arorasoham9/Embedded-C--ARM-M0-Cortex-Maze-game/src/wavetable.c

#include <math.h>

#include "midiplay.h"

short int wavetable[N];

// sine wave
void init_wavetable_sine(void) {
    int x;
    for(x=0; x<N; x++) {
        wavetable[x] = 32767 * sin(2 * M_PI * x / N);
    }
}

// sawtooth wave
void init_wavetable_sawtooth(void) {
    int x;
    for(x=0; x<N; x++)
        wavetable[x] = 32767.0 * (x - N/2) / (1.0*N);
}

// square wave
void init_wavetable_square(void) {
    int x;
    for(x=0; x<N; x++)
        if (x < N/2)
            wavetable[x] = -32767;
        else
            wavetable[x] = 32767;
}

// 1/2 amplitude sine wave added to 1/2 amplitude sawtooth wave
void init_wavetable_hybrid(void) {
    int x;
    for(x=0; x<N; x++)
        wavetable[x] = 16383 * sin(2 * M_PI * x / N) + 16383.0 * (x - N/2) / (1.0*N);
}

// 3/4 amplitude sine wave added to 1/4 amplitude sawtooth wave
void init_wavetable_hybrid2(void) {
    int x;
    for(x=0; x<N; x++)
        wavetable[x] = 3*8191 * sin(2 * M_PI * x / N) + 8191.0 * (x - N/2) / (1.0*N);
}
